samechikson/open-putt/microcontroller/blink/blink.ino

// Blink test — confirms compile -> upload -> run works on the ELEGOO ESP32.
// Onboard LED is on GPIO2 for this WROOM-32 dev board.

const int LED_PIN = 2;

void setup() {
  pinMode(LED_PIN, OUTPUT);
  Serial.begin(115200);
  Serial.println("ESP32 blink test starting");
}

void loop() {
  digitalWrite(LED_PIN, HIGH);
  Serial.println("LED ON");
  delay(1000);
  digitalWrite(LED_PIN, LOW);
  Serial.println("LED OFF");
  delay(1000);
}
